LieBtrau/esp32-web-radio/info/pictures/IMG_20240320_211419_235.jpg

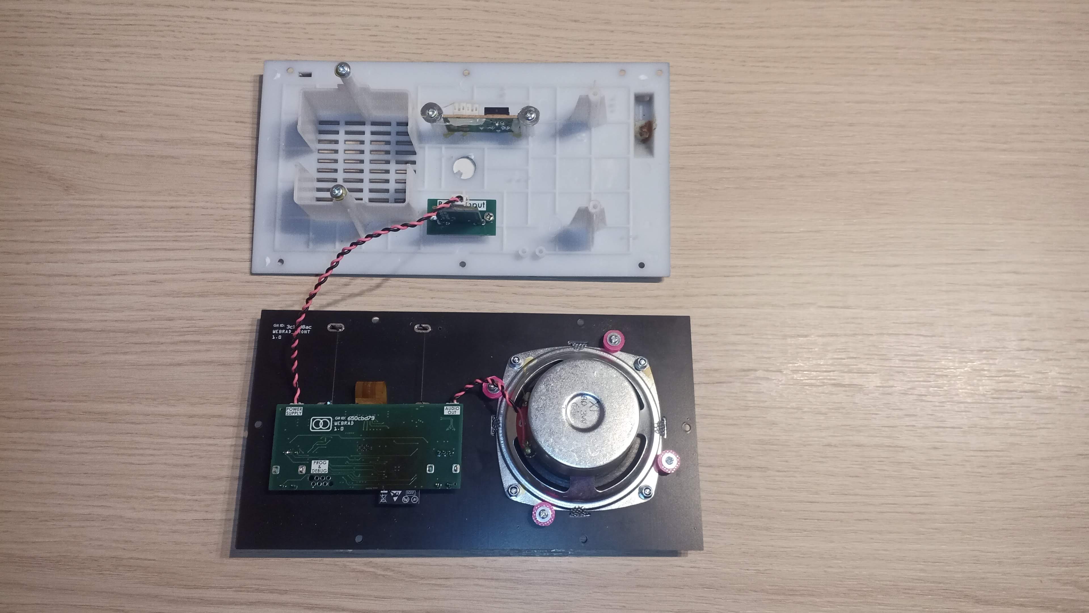
info/pictures/IMG_20240320_211419_235.jpg
