LieBtrau/esp32-web-radio/info/pictures/IMG_20240320_211535_679.jpg

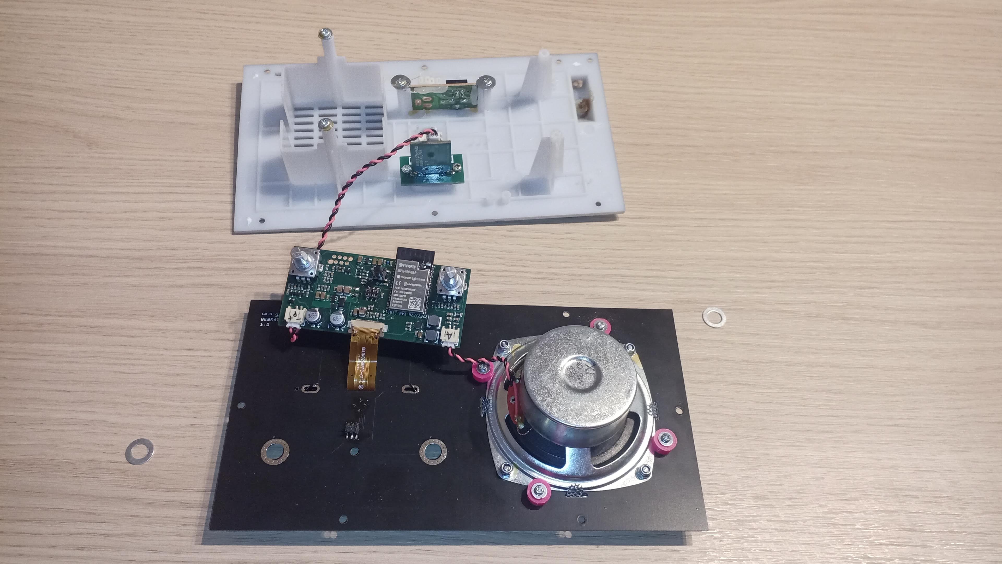
info/pictures/IMG_20240320_211535_679.jpg
