LieBtrau/esp32-web-radio/info/pictures/IMG_20240320_212915_946.jpg

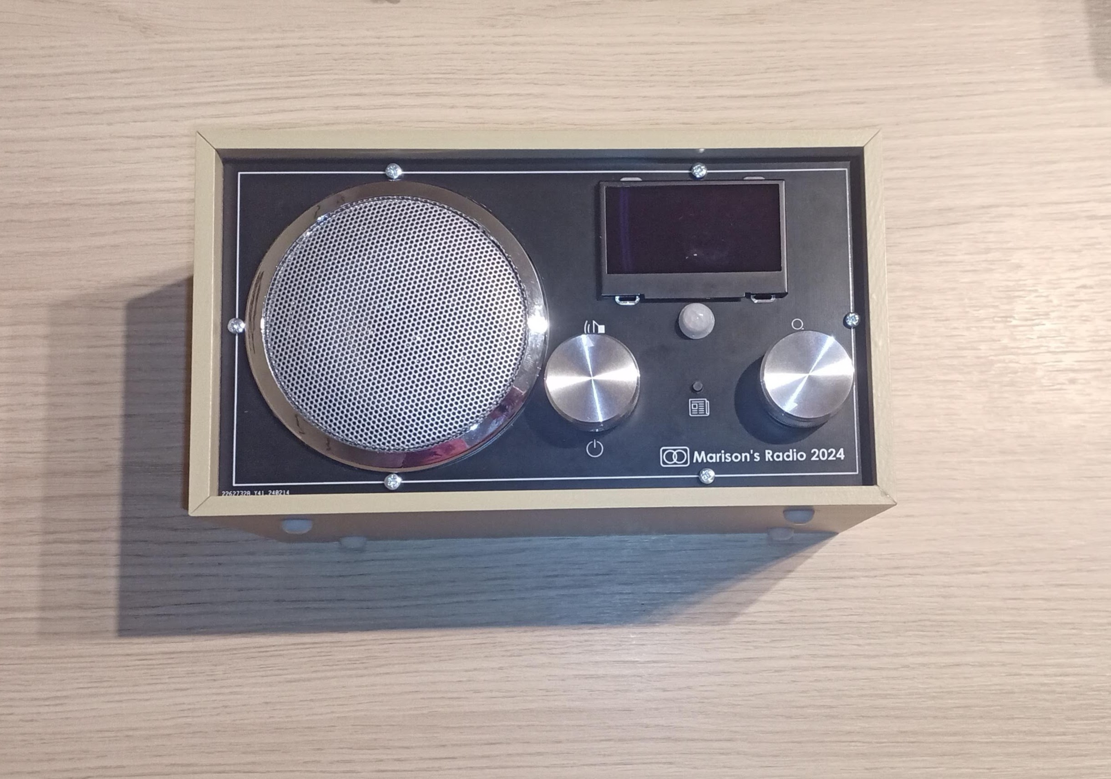
info/pictures/IMG_20240320_212915_946.jpg
