LieBtrau/esp32-web-radio/info/pictures/IMG_20240320_213904_540.jpg

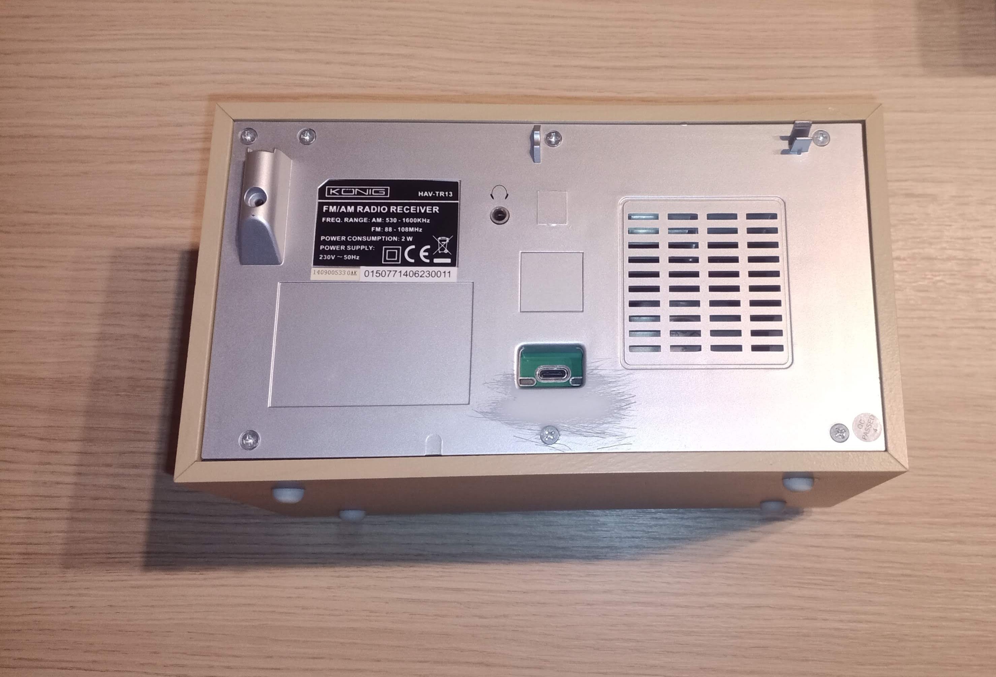
info/pictures/IMG_20240320_213904_540.jpg
