LieBtrau/esp32-web-radio/info/pictures/IMG_20240320_214232_546.jpg

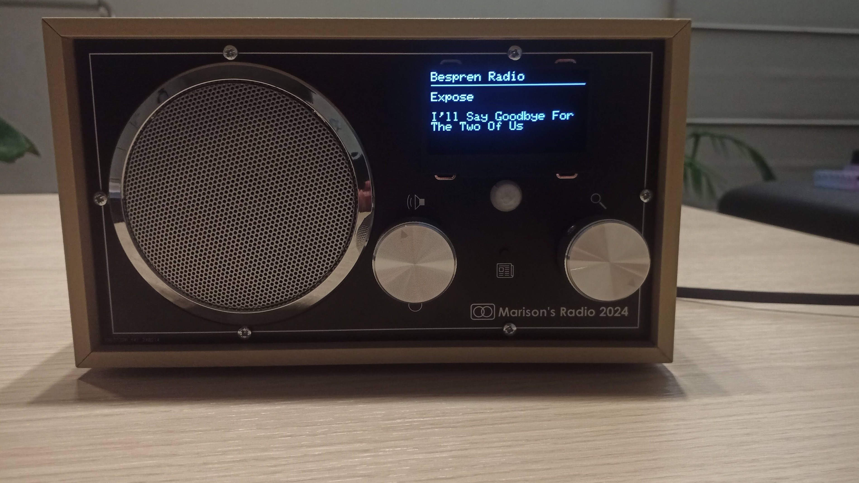
info/pictures/IMG_20240320_214232_546.jpg
