LieBtrau/esp32-web-radio/hardware/simulations/booster_power_sequencer.asc

M1: pmos; AO3401A
R1: res; 3.3k
R2: res; 5k
R3: res; 3.3k
R4: res; 100k
R5: res; 100
U1: TLV431
V1: voltage; 5
V2: voltage; PWL(0 0 50m 3.3 100m 0)
Named nets: 0, OUT
.inc "AO3401A.mod"
.tran 100m
