LieBtrau/esp32-web-radio/hardware/simulations/ClassDfilter.asc

C1: cap; 680n
C2: cap; 2µ
C3: cap; 50p
C4: cap; 1µ
C5: cap; 100n
C6: cap; 100n
L1: ind; 22e-6; Rser=0.1
L2: ind; 23µH
L3: ind; 22e-6; Rser=0.1
L4: ind; 22e-6; Rser=0.1
R1: res; 4
R2: res; 3.3
R3: res; 8
R4: res; 1k
V1: voltage; ""; AC 1
V2: voltage; ""; AC 1
Named nets: 0, OUT1
.ac dec 100 1 10e6
https://www.edn.com/understanding-output-filters-for-class-d-amplifiers/
