LieBtrau/esp32-web-radio/hardware/simulations/speaker_impedance.asc

C1: cap; 50p
I1: current; ""; AC 1
L1: ind; 23µH
R1: res; 8
R2: res; 1k
Named nets: 0
.ac dec 101 50k 10meg
