LieBtrau/esp32-web-radio/firmware/esp32/platformio/esp32-web-radio/src/Music.cpp

#include "Music.h"

static const char *TAG = "Music";
extern void showstreamtitle(const String& artist, const String& song_title);

Music::Music(const int i2c_sda, const int i2c_scl, const int pin_PA_enable)
#ifdef ESP32_AUDIO_KIT
    : _i2c_sda(i2c_sda), _i2c_scl(i2c_scl), _pin_PA_enable(pin_PA_enable), _dac(ES8388(_i2c_sda, _i2c_scl))
#endif
{
}

Music::~Music()
{
    // free allocated heap memory
}

bool Music::init(const uint8_t i2s_bck, const uint8_t i2s_ws, const uint8_t i2s_data_out)
{
    if (!_audio.setPinout(i2s_bck, i2s_ws, i2s_data_out))
    {
        ESP_LOGE(TAG,"Error setting pinout");
        return false;
    }
#ifdef ESP32_AUDIO_KIT
    if (!dac.init())
    {
        ESP_LOGE(TAG,"Error initializing ES8388 chip");
        return false;
    }
    _dac.setOutputVolume(ES8388::OutSel::OUTALL, _volume);
    if (_pin_PA_enable != -1)
    {
        pinMode(_pin_PA_enable, OUTPUT);
        digitalWrite(_pin_PA_enable, HIGH);
    }
#endif
    _audio.setVolume(_volume);
    return true;
}

bool Music::playSpeech(const char *text, const char *lang, bool isBlocking)
{
    if (_audio.isRunning())
    {
        ESP_LOGW(TAG, "Already playing");
        return false;
    }
    if (!isBlocking)
    {
        return _audio.connecttospeech(text, lang);
    }
    else
    {
        if (!_audio.connecttospeech(text, lang))
        {
            return false;
        }
        while (_audio.isRunning())
        {
            _audio.loop();
            delay(1);
        }
        return true;
    }
}

bool Music::startStream(const char *url, const uint8_t volume,  bool stopCurrentAudio)
{
    if (_audio.isRunning() && !stopCurrentAudio)
    {
        ESP_LOGW(TAG, "Already playing");
        return false;
    }
    if(!setVolume(volume))
    {
        ESP_LOGE(TAG,"Error setting volume");
        return false;
    }
    return _audio.connecttohost(url);
}

bool Music::stopStream()
{
    if (!_audio.isRunning())
    {
        ESP_LOGW(TAG, "Not playing");
        return false;
    }
    return _audio.stopSong();
}

void Music::update()
{
    _audio.loop();
}

bool Music::isPlaying()
{
    return _audio.isRunning();
}

bool Music::increaseVolume()
{
#ifdef ESP32_AUDIO_KIT
    uint8_t new_volume = _dac.getOutputVolume() + 1;
#else
    uint8_t new_volume = _audio.getVolume() + 1;
#endif
    return setVolume(new_volume);
}

bool Music::decreaseVolume()
{
#ifdef ESP32_AUDIO_KIT
    uint8_t new_volume = _dac.getOutputVolume() > 0 ? dac.getOutputVolume() - 1 : 0;
#else
    uint8_t new_volume = _audio.getVolume() > 0 ? _audio.getVolume() - 1 : 0;
#endif
    return setVolume(new_volume);
}

bool Music::setVolume(const uint8_t volume)
{
#ifdef ESP32_AUDIO_KIT
    _dac.setOutputVolume(ES8388::OutSel::OUTALL, volume);
    return volume == _dac.getOutputVolume();
#else
    _audio.setVolume(volume);
    return volume == _audio.getVolume();
#endif
}

uint8_t Music::getVolume() 
{
#ifdef ESP32_AUDIO_KIT
    return _dac.getOutputVolume();
#else
    return _audio.getVolume();
#endif
}

uint8_t Music::getMaxValue() const
{
#ifdef ESP32_AUDIO_KIT
    return _dac.getMaxVolume();
#else
    return 21;
#endif
}

/**
 * @brief Callback function for audio library
 * 
 * @param info string that contains the stream info : artist - song title
 */
void audio_showstreamtitle(const char *info)
{
    const char *SPLIT = " - ";
    char artist[40]={0}, song_title[40]={0};
    char *splitstart = strstr(info, SPLIT);

    ESP_LOGI(TAG, "Stream info: %s", info);

    if (splitstart != NULL)
    {
        // Get artist
        int artist_length = splitstart - info;
        strncpy(artist, info, min(40, artist_length));
        artist[artist_length] = '\0';
        ESP_LOGI(TAG, "Artist : %s.\r\n", artist);

        // Get song title
        int song_length = strlen(info) - strlen(artist) - strlen(SPLIT);
        if (song_length > 0)
        {
            strncpy(song_title, splitstart + strlen(SPLIT), min(40, song_length));
            song_title[song_length] = '\0';
            ESP_LOGI(TAG, "Song : %s.\r\n", song_title);

            showstreamtitle(String(artist), String(song_title));
        }
    }
    else
    {
        ESP_LOGI(TAG, "No split found");
        showstreamtitle(String(info), String(""));
    }
}

void audio_eof_mp3(const char *info)
{
    ESP_LOGI(TAG, "End of file");
}

// optional
void audio_info(const char *info)
{
    ESP_LOGI(TAG, "info: %s", info);
}
void audio_id3data(const char *info)
{ // id3 metadata
    ESP_LOGI(TAG, "id3data: %s", info);
}

void audio_showstation(const char *info)
{
    ESP_LOGI(TAG, "Station: %s", info);
}

void audio_bitrate(const char *info)
{
    ESP_LOGI(TAG, "Bitrate: %s", info);
}
void audio_commercial(const char *info)
{ // duration in sec
    ESP_LOGI(TAG, "commercial: %s", info);
}
void audio_icyurl(const char *info)
{ // homepage
    ESP_LOGI(TAG, "icyurl: %s", info);
}
void audio_lasthost(const char *info)
{ // stream URL played
    ESP_LOGI(TAG, "lasthost: %s", info);
}
void audio_eof_speech(const char *info)
{
    ESP_LOGI(TAG, "End of speech: %s", info);
}
