LieBtrau/esp32-web-radio/firmware/esp32/platformio/tests/LcdMenuLib2/src/main.cpp

// ============================================================
// Example:     LCDML: use ADAFRUIT i2c display ssd1306
// ============================================================
// Author:      Jomelo
// Last update: 12.11.2018
// License:     MIT
// ============================================================
// Description:
// This example shows how to use the adafruit gfx library
// with the LCDMenuLib.
// The menu can placed in a box that can be placed anywhere on
// the screen.
// ============================================================
// *********************************************************************
// special settings
// *********************************************************************
// enable this line when you are not usigng a standard arduino
// for example when your chip is an ESP or a STM or SAM or something else

#define _LCDML_cfg_use_ram

// include libs
#include <LCDMenuLib2.h>

#include <SPI.h>
#include <Wire.h>
#include <Adafruit_GFX.h>
#include <Adafruit_SSD1305.h>
#include "LCDdefines.h"

// *********************************************************************
// Prototypes
// *********************************************************************
void lcdml_menu_display();
void lcdml_menu_clear();
void lcdml_menu_control();
extern void mFunc_information(uint8_t param);
extern void mFunc_timer_info(uint8_t param);
extern void mFunc_back(uint8_t param);
extern void mFunc_jumpTo_timer_info(uint8_t param);
extern void mFunc_p2(uint8_t param);
extern void mFunc_goToRootMenu(uint8_t param);
extern void mFunc_para(uint8_t param);
extern void mDyn_para(uint8_t line);
extern void mFunc_screensaver(uint8_t param);
extern boolean COND_hide();

// *********************************************************************
// Objects
// *********************************************************************
LCDMenuLib2_menu LCDML_0(255, 0, 0, NULL, NULL); // root menu element (do not change)
LCDMenuLib2 LCDML(LCDML_0, _LCDML_DISP_rows, _LCDML_DISP_cols, lcdml_menu_display, lcdml_menu_clear, lcdml_menu_control);
static const char *TAG = "main";
TwoWire i2c = TwoWire(1);
const int OLED_RESET = 5;
Adafruit_SSD1305 display(_LCDML_ADAFRUIT_lcd_w, _LCDML_ADAFRUIT_lcd_h, &i2c, OLED_RESET);

// *********************************************************************
// LCDML MENU/DISP
// *********************************************************************
// LCDML_0        => layer 0
// LCDML_0_X      => layer 1
// LCDML_0_X_X    => layer 2
// LCDML_0_X_X_X  => layer 3
// LCDML_0_...      => layer ...

// For beginners
// LCDML_add(id, prev_layer, new_num, lang_char_array, callback_function)
LCDML_add(0, LCDML_0, 1, "Information", mFunc_information);                // this menu function can be found on "LCDML_display_menuFunction" tab
LCDML_add(1, LCDML_0, 2, "Time info", mFunc_timer_info);                   // this menu function can be found on "LCDML_display_menuFunction" tab
LCDML_add(2, LCDML_0, 3, "Program", NULL);                                 // NULL = no menu function
LCDML_add(3, LCDML_0_3, 1, "Program 1", NULL);                             // NULL = no menu function
LCDML_add(4, LCDML_0_3_1, 1, "P1 dummy", NULL);                            // NULL = no menu function
LCDML_add(5, LCDML_0_3_1, 2, "P1 Settings", NULL);                         // NULL = no menu function
LCDML_add(6, LCDML_0_3_1_2, 1, "Warm", NULL);                              // NULL = no menu function
LCDML_add(7, LCDML_0_3_1_2, 2, "Cold", NULL);                              // NULL = no menu function
LCDML_add(8, LCDML_0_3_1_2, 3, "Back", mFunc_back);                        // this menu function can be found on "LCDML_display_menuFunction" tab
LCDML_add(9, LCDML_0_3_1, 3, "Back", mFunc_back);                          // this menu function can be found on "LCDML_display_menuFunction" tab
LCDML_add(10, LCDML_0_3, 2, "Program 2", mFunc_p2);                        // this menu function can be found on "LCDML_display_menuFunction" tab
LCDML_add(11, LCDML_0_3, 3, "Back", mFunc_back);                           // this menu function can be found on "LCDML_display_menuFunction" tab
LCDML_add(12, LCDML_0, 4, "Special", NULL);                                // NULL = no menu function
LCDML_add(13, LCDML_0_4, 1, "Go to Root", mFunc_goToRootMenu);             // this menu function can be found on "LCDML_display_menuFunction" tab
LCDML_add(14, LCDML_0_4, 2, "Jump to Time info", mFunc_jumpTo_timer_info); // this menu function can be found on "LCDML_display_menuFunction" tab
LCDML_add(15, LCDML_0_4, 3, "Back", mFunc_back);                           // this menu function can be found on "LCDML_display_menuFunction" tab

// Advanced menu (for profit) part with more settings
// Example for one function and different parameters
// It is recommend to use parameters for switching settings like, (small drink, medium drink, big drink) or (200ml, 400ml, 600ml, 800ml) ...
// the parameter change can also be released with dynParams on the next example
// LCDMenuLib_addAdvanced(id, prev_layer,     new_num, condition,   lang_char_array, callback_function, parameter (0-255), menu function type  )
LCDML_addAdvanced(16, LCDML_0, 5, NULL, "Parameter", NULL, 0, _LCDML_TYPE_default);            // NULL = no menu function
LCDML_addAdvanced(17, LCDML_0_5, 1, NULL, "Parameter 1", mFunc_para, 10, _LCDML_TYPE_default); // NULL = no menu function
LCDML_addAdvanced(18, LCDML_0_5, 2, NULL, "Parameter 2", mFunc_para, 20, _LCDML_TYPE_default); // NULL = no menu function
LCDML_addAdvanced(19, LCDML_0_5, 3, NULL, "Parameter 3", mFunc_para, 30, _LCDML_TYPE_default); // NULL = no menu function
LCDML_add(20, LCDML_0_5, 4, "Back", mFunc_back);                                               // this menu function can be found on "LCDML_display_menuFunction" tab

// Example for dynamic content
// 1. set the string to ""
// 2. use type  _LCDML_TYPE_dynParam   instead of    _LCDML_TYPE_default
// this function type can not be used in combination with different parameters
// LCDMenuLib_addAdvanced(id, prev_layer,     new_num, condition,   lang_char_array, callback_function, parameter (0-255), menu function type  )
LCDML_addAdvanced(21, LCDML_0, 6, NULL, "", mDyn_para, 0, _LCDML_TYPE_dynParam); // NULL = no menu function

// Example for conditions (for example for a screensaver)
// 1. define a condition as a function of a boolean type -> return false = not displayed, return true = displayed
// 2. set the function name as callback (remove the braces '()' it gives bad errors)
// LCDMenuLib_addAdvanced(id, prev_layer,     new_num, condition,   lang_char_array, callback_function, parameter (0-255), menu function type  )
LCDML_addAdvanced(22, LCDML_0, 7, COND_hide, "screensaver", mFunc_screensaver, 0, _LCDML_TYPE_default); // this menu function can be found on "LCDML_display_menuFunction" tab

// ***TIP*** Try to update _LCDML_DISP_cnt when you add a menu element.

// menu element count - last element id
// this value must be the same as the last menu element
#define _LCDML_DISP_cnt 22

// create menu
LCDML_createMenu(_LCDML_DISP_cnt);

// *********************************************************************
// SETUP
// *********************************************************************
void setup()
{
  // serial init; only be needed if serial control is used
  Serial.begin(115200);                // start serial
  Serial.println(F(_LCDML_VERSION)); // only for examples

  /* INIT DISPLAY */
  // initialize with the I2C addr / mit I2C-Adresse initialisieren
  ESP_LOGI(TAG, "\r\nBuild %s, utc: %lu\r\n", COMMIT_HASH, CURRENT_TIME);
  i2c.begin(18, 23, 100000);
  Serial.println("SSD1305 OLED test");
  
  if ( ! display.begin(_ADAFRUIT_I2C_ADR) ) {
     Serial.println("Unable to initialize OLED");
     while (1) yield();
  }

  // clear lcd
  display.clearDisplay();
  // set text color / Textfarbe setzen
  display.setTextColor(_LCDML_ADAFRUIT_TEXT_COLOR);
  // set text size / Textgroesse setzen
  display.setTextSize(_LCDML_ADAFRUIT_FONT_SIZE);
  display.setCursor(0, _LCDML_ADAFRUIT_FONT_H * (3));
  display.println("LCDMenuLib v2.1.4 alpha");
  display.display();

  /* INIT LCDML */
  // LCDMenuLib Setup
  LCDML_setup(_LCDML_DISP_cnt);

  // Enable Menu Rollover
  LCDML.MENU_enRollover();

  // Enable Screensaver (screensaver menu function, time to activate in ms)
  LCDML.SCREEN_enable(mFunc_screensaver, 10000); // set to 10 seconds
  // LCDML.SCREEN_disable();

  // Some needful methods

  // You can jump to a menu function from anywhere with
  // LCDML.OTHER_jumpToFunc(mFunc_p2); // the parameter is the function name
}

// *********************************************************************
// LOOP
// *********************************************************************
void loop()
{
  // this function must called here, do not delete it
  LCDML.loop();
}

// *********************************************************************
// check some errors - do not change here anything
// *********************************************************************
#if (_LCDML_glcd_tft_box_x1 > _LCDML_glcd_tft_w)
#error _LCDML_glcd_tft_box_x1 is to big
#endif

#if (_LCDML_glcd_tft_box_y1 > _LCDML_glcd_tft_h)
#error _LCDML_glcd_tft_box_y1 is to big
#endif
