LieBtrau/esp32-web-radio/firmware/esp32/platformio/tests/LcdMenuLib2/include/LCDdefines.h

#define _ADAFRUIT_I2C_ADR 0x3C
#define _LCDML_ADAFRUIT_TEXT_COLOR WHITE

#define _LCDML_ADAFRUIT_FONT_SIZE 1
#define _LCDML_ADAFRUIT_FONT_W (6 * _LCDML_ADAFRUIT_FONT_SIZE) // font width
#define _LCDML_ADAFRUIT_FONT_H (8 * _LCDML_ADAFRUIT_FONT_SIZE) // font heigt

// settings for u8g lib and lcd
#define _LCDML_ADAFRUIT_lcd_w 128 // lcd width
#define _LCDML_ADAFRUIT_lcd_h 64  // lcd height

// nothing change here
#define _LCDML_ADAFRUIT_cols_max (_LCDML_ADAFRUIT_lcd_w / _LCDML_ADAFRUIT_FONT_W)
#define _LCDML_ADAFRUIT_rows_max (_LCDML_ADAFRUIT_lcd_h / _LCDML_ADAFRUIT_FONT_H)

// rows and cols
// when you use more rows or cols as allowed change in LCDMenuLib.h the define "_LCDML_DISP_cfg_max_rows" and "_LCDML_DISP_cfg_max_string_length"
// the program needs more ram with this changes
#define _LCDML_ADAFRUIT_cols 20                       // max cols
#define _LCDML_ADAFRUIT_rows _LCDML_ADAFRUIT_rows_max // max rows

// scrollbar width
#define _LCDML_ADAFRUIT_scrollbar_w 6 // scrollbar width

// old defines with new content
#define _LCDML_DISP_cols _LCDML_ADAFRUIT_cols
#define _LCDML_DISP_rows _LCDML_ADAFRUIT_rows
