LieBtrau/esp32-web-radio/firmware/esp32/platformio/tests/o-led-test/src/main.cpp

#include <Adafruit_SSD1305.h>
#include "pins.h"

static const char *TAG = "main";
const int OLED_RESET = 5;
Adafruit_SSD1305 display(128, 64, &Wire, OLED_RESET);

#define NUMFLAKES 10
#define XPOS 0
#define YPOS 1
#define DELTAY 2

#define LOGO16_GLCD_HEIGHT 16
#define LOGO16_GLCD_WIDTH 16
static const unsigned char PROGMEM logo16_glcd_bmp[] =
    {B00000000, B11000000,
     B00000001, B11000000,
     B00000001, B11000000,
     B00000011, B11100000,
     B11110011, B11100000,
     B11111110, B11111000,
     B01111110, B11111111,
     B00110011, B10011111,
     B00011111, B11111100,
     B00001101, B01110000,
     B00011011, B10100000,
     B00111111, B11100000,
     B00111111, B11110000,
     B01111100, B11110000,
     B01110000, B01110000,
     B00000000, B00110000};

void testdrawbitmap(const uint8_t *bitmap, uint8_t w, uint8_t h)
{
  uint8_t icons[NUMFLAKES][3];
  randomSeed(666); // whatever seed

  // initialize
  for (uint8_t f = 0; f < NUMFLAKES; f++)
  {
    icons[f][XPOS] = random(display.width());
    icons[f][YPOS] = 0;
    icons[f][DELTAY] = random(5) + 1;

    Serial.print("x: ");
    Serial.print(icons[f][XPOS], DEC);
    Serial.print(" y: ");
    Serial.print(icons[f][YPOS], DEC);
    Serial.print(" dy: ");
    Serial.println(icons[f][DELTAY], DEC);
  }

  while (1)
  {
    // draw each icon
    for (uint8_t f = 0; f < NUMFLAKES; f++)
    {
      display.drawBitmap(icons[f][XPOS], icons[f][YPOS], logo16_glcd_bmp, w, h, WHITE);
    }
    display.display();
    delay(200);

    // then erase it + move it
    for (uint8_t f = 0; f < NUMFLAKES; f++)
    {
      display.drawBitmap(icons[f][XPOS], icons[f][YPOS], logo16_glcd_bmp, w, h, BLACK);
      // move it
      icons[f][YPOS] += icons[f][DELTAY];
      // if its gone, reinit
      if (icons[f][YPOS] > display.height())
      {
        icons[f][XPOS] = random(display.width());
        icons[f][YPOS] = 0;
        icons[f][DELTAY] = random(5) + 1;
      }
    }
  }
}

void testdrawchar(void)
{
  display.clearDisplay();
  display.setTextSize(1);
  display.setTextWrap(false);
  display.setTextColor(WHITE);
  display.setCursor(0, 0);
  display.cp437(true);  // true code page 437 (without Adafruit bug, see https://learn.adafruit.com/adafruit-gfx-graphics-library/graphics-primitives

  for (uint8_t i = 0; i < 168; i++)
  {
    if (i == '\n')
      continue;
    display.write(i%2 ? '\xDB' : '\xB0');
    if ((i > 0) && (i % 21 == 0))
      display.println();
  }
  display.display();
}

void setup()
{
  ESP_LOGI(TAG, "\r\nBuild %s, utc: %lu\r\n", COMMIT_HASH, CURRENT_TIME);
  Wire.setPins(PIN_SDA, PIN_SCL);

  if (!display.begin(0x3C))
  {
    Serial.println("Unable to initialize OLED");
    while (1)
      yield();
  }
  
  testdrawchar();
  return;

  for (uint8_t rot = 0; rot < 4; rot++)
  {
    display.setRotation(rot);
    display.clearDisplay();
    // text display tests
    display.setTextSize(1);
    display.setTextColor(WHITE);
    display.setCursor(0,0);
    display.println("Hello, world!");
    display.setTextColor(BLACK, WHITE); // 'inverted' text
    display.println(3.141592);
    display.setTextSize(2);
    display.setTextColor(WHITE);
    display.print("0x"); display.println(0xDEADBEEF, HEX);
    display.display();
    delay(1000);
  }

  display.setRotation(0);

  // miniature bitmap display
  display.clearDisplay();
  display.drawBitmap(30, 16, logo16_glcd_bmp, 16, 16, 1);
  display.display();

  // invert the display
  display.invertDisplay(true);
  delay(1000);
  display.invertDisplay(false);
  delay(1000);

  // draw a bitmap icon and 'animate' movement
  testdrawbitmap(logo16_glcd_bmp, LOGO16_GLCD_HEIGHT, LOGO16_GLCD_WIDTH);
}

void loop()
{
  // put your main code here, to run repeatedly:
}
