LieBtrau/esp32-web-radio/firmware/esp32/platformio/tests/rotary_encoder_test/src/main.cpp

#include <Arduino.h>
#include "RotaryEncoder.h"
#include "pins.h"


static const char *TAG = "main";
static Encoder encoder1(PIN_S1, PIN_S2);
static RotaryEncoder encoder(&encoder1);

void setup()
{
  ESP_LOGI(TAG, "\r\nBuild %s, utc: %lu\r\n", COMMIT_HASH, CURRENT_TIME);
}

int lastpos = 0;
void loop()
{
  switch (encoder.rotary_encoder_update())
  {
  case RotaryEncoder::TURN_DOWN:
    lastpos--;
    ESP_LOGI(TAG, "lastpos: %d", lastpos);
    break;
  case RotaryEncoder::TURN_UP:
    lastpos++;
    ESP_LOGI(TAG, "lastpos: %d", lastpos);
    break;
  default:
    break;
  }
}
