LieBtrau/esp32-web-radio/firmware/esp32/platformio/tests/LcdMenuLib2/src/LCDML_display_menu.cpp

// =====================================================================
//
// Output function
//
// =====================================================================

#include "LCDMenuLib2.h"
#include "Adafruit_SSD1305.h"
#include "LCDdefines.h"

extern Adafruit_SSD1305 display;
extern LCDMenuLib2 LCDML;

/* ******************************************************************** */
void lcdml_menu_clear()
/* ******************************************************************** */
{
}

/* ******************************************************************** */
void lcdml_menu_display()
/* ******************************************************************** */
{
  // clear lcd
  display.clearDisplay();
  // set text color / Textfarbe setzen
  display.setTextColor(_LCDML_ADAFRUIT_TEXT_COLOR);  
  // set text size / Textgroesse setzen
  display.setTextSize(_LCDML_ADAFRUIT_FONT_SIZE);

  
  // declaration of some variables
  // ***************
  // content variable
  char content_text[_LCDML_DISP_cols];  // save the content text of every menu element
  // menu element object
  LCDMenuLib2_menu *tmp;
  // some limit values
  uint8_t i = LCDML.MENU_getScroll();
  uint8_t maxi = _LCDML_DISP_rows + i;
  uint8_t n = 0;

   // init vars
  uint8_t n_max             = (LCDML.MENU_getChilds() >= _LCDML_DISP_rows) ? _LCDML_DISP_rows : (LCDML.MENU_getChilds());

  uint8_t scrollbar_min     = 0;
  uint8_t scrollbar_max     = LCDML.MENU_getChilds();
  uint8_t scrollbar_cur_pos = LCDML.MENU_getCursorPosAbs();
  uint8_t scroll_pos        = ((1.*n_max * _LCDML_DISP_rows) / (scrollbar_max - 1) * scrollbar_cur_pos);


  n = 0;
  i = LCDML.MENU_getScroll();
  // update content
  // ***************

    // clear menu
    // ***************

  // check if this element has children
  if ((tmp = LCDML.MENU_getDisplayedObj()) != NULL)
  {
    // loop to display lines
    do
    {
      // check if a menu element has a condition and if the condition be true
      if (tmp->checkCondition())
      {
        // check the type off a menu element
        if(tmp->checkType_menu() == true)
        {
          // display normal content
          //LCDML_getContent(content_text, tmp->getID()); //function not found
          display.setCursor(1, _LCDML_ADAFRUIT_FONT_H * (n));
          display.println(content_text);
        }
        else
        {
          if(tmp->checkType_dynParam()) {
            tmp->callback(n);
          }
        }
        // increment some values
        i++;
        n++;
      }
    // try to go to the next sibling and check the number of displayed rows
    } while (((tmp = tmp->getSibling(1)) != NULL) && (i < maxi));
  }

  // set cursor
  display.setCursor(0, _LCDML_ADAFRUIT_FONT_H * (LCDML.MENU_getCursorPos()));
  display.println("X");

  // ***** todo *****
  #ifdef _SCROLLBAR_TODO_
  if(_LCDML_DISP_draw_frame == 1) {
     u8g2.drawFrame(_LCDML_DISP_box_x0, _LCDML_DISP_box_y0, (_LCDML_DISP_box_x1-_LCDML_DISP_box_x0), (_LCDML_DISP_box_y1-_LCDML_DISP_box_y0));
  }

  
  // display scrollbar when more content as rows available and with > 2
  
  if (scrollbar_max > n_max && _LCDML_DISP_scrollbar_w > 2)
  {
    // set frame for scrollbar
    //u8g2.drawFrame(_LCDML_DISP_box_x1 - _LCDML_DISP_scrollbar_w, _LCDML_DISP_box_y0, _LCDML_DISP_scrollbar_w, _LCDML_DISP_box_y1-_LCDML_DISP_box_y0);
    display.drawRect(_LCDML_ADAFRUIT_lcd_w - _LCDML_ADAFRUIT_scrollbar_w, 0,_LCDML_ADAFRUIT_scrollbar_w,_LCDML_ADAFRUIT_lcd_h, _LCDML_ADAFRUIT_TEXT_COLOR); 

    // calculate scrollbar length
    uint8_t scrollbar_block_length = scrollbar_max - n_max;
    scrollbar_block_length = (_LCDML_DISP_box_y1-_LCDML_DISP_box_y0) / (scrollbar_block_length + _LCDML_DISP_rows);

    //set scrollbar
    if (scrollbar_cur_pos == 0) {                                   // top position     (min)
      u8g2.drawBox(_LCDML_DISP_box_x1 - (_LCDML_DISP_scrollbar_w-1), _LCDML_DISP_box_y0 + 1                                                     , (_LCDML_DISP_scrollbar_w-2)  , scrollbar_block_length);
    }
    else if (scrollbar_cur_pos == (scrollbar_max-1)) {            // bottom position  (max)
      u8g2.drawBox(_LCDML_DISP_box_x1 - (_LCDML_DISP_scrollbar_w-1), _LCDML_DISP_box_y1 - scrollbar_block_length                                , (_LCDML_DISP_scrollbar_w-2)  , scrollbar_block_length);
    }
    else {                                                                // between top and bottom
      u8g2.drawBox(_LCDML_DISP_box_x1 - (_LCDML_DISP_scrollbar_w-1), _LCDML_DISP_box_y0 + (scrollbar_block_length * scrollbar_cur_pos + 1),(_LCDML_DISP_scrollbar_w-2)  , scrollbar_block_length);
    }
  }
  #endif

  display.display();
  
}
