LieBtrau/esp32-web-radio/firmware/esp32/platformio/tests/LcdMenuLib2/src/LCDML_condition.cpp

/* ===================================================================== *
 *                                                                       *
 * Conditions to show or hide a menu element on the display              *
 *                                                                       *
 * ===================================================================== *
 */
#include "LCDMenuLib2.h"

// *********************************************************************
boolean COND_hide()  // hide a menu element
// ********************************************************************* 
{ 
  return false;  // hidden
} 
